mwuerms/tinytimer/microchip-studio/tinytimer/buttons.c

/**
 * Martin Egli
 * 2023-03-21
 * module timer
 */

#include <util/atomic.h>
#include <avr/interrupt.h>
#include "project.h"
#include "io.h"
#include "buttons.h"
#include "rtc.h"
#include "leds.h"

enum {
	BUTTON_NONE = 0,
	BUTTON_PRESSED,
	BUTTON_RELEASED
};
static volatile uint8_t button_last_state[NB_BUTTONS];

ISR(PORTA_PORT_vect) {
	if(BUTTON1_PORT.INTFLAGS & BUTTON1_PIN_BV) {
		BUTTON1_PORT.INTFLAGS |= BUTTON1_PIN_BV; // clr
		if(BUTTON1_PORT.IN & BUTTON1_PIN_BV) {
			button_last_state[BUTTON1] = BUTTON_RELEASED;
		}
		else {
			button_last_state[BUTTON1] = BUTTON_PRESSED;
		}
	}
	if(BUTTON2_PORT.INTFLAGS & BUTTON2_PIN_BV) {
		BUTTON2_PORT.INTFLAGS |= BUTTON2_PIN_BV; // clr
		if(BUTTON2_PORT.IN & BUTTON2_PIN_BV) {
			button_last_state[BUTTON2] = BUTTON_RELEASED;
		}
		else {
			button_last_state[BUTTON2] = BUTTON_PRESSED;
		}
	}
	global_events |= EV_BUTTON;
}

ISR(PORTB_PORT_vect) {
	if(BUTTON3_PORT.INTFLAGS & BUTTON3_PIN_BV) {
		BUTTON3_PORT.INTFLAGS |= BUTTON3_PIN_BV; // clr
		if(BUTTON3_PORT.IN & BUTTON3_PIN_BV) {
			button_last_state[BUTTON3] = BUTTON_RELEASED;
		}
		else {
			button_last_state[BUTTON3] = BUTTON_PRESSED;
		}
	}
	if(BUTTON4_PORT.INTFLAGS & BUTTON4_PIN_BV) {
		BUTTON4_PORT.INTFLAGS |= BUTTON4_PIN_BV; // clr
		if(BUTTON4_PORT.IN & BUTTON4_PIN_BV) {
			button_last_state[BUTTON4] = BUTTON_RELEASED;
		}
		else {
			button_last_state[BUTTON4] = BUTTON_PRESSED;
		}
	}
	global_events |= EV_BUTTON;
}

/* all buttons
 * input
 * pullup
 * interrupt on both edges
 * button pressed =  low,  falling edge
 * button released = high, rising edge
 */
#define PORT_INT_DISABLE	0
#define PORT_INT_BOTH_EDGES	1
void buttons_Init(void) {
	BUTTON1_PORT.DIRCLR = BUTTON1_PIN_BV;	// input
	BUTTON1_PORT.BUTTON1_PIN_CTRL = PORT_PULLUPEN_bm | PORT_INT_BOTH_EDGES;	// pullup, int on both edges
	
	BUTTON2_PORT.DIRCLR = BUTTON2_PIN_BV;
	BUTTON2_PORT.BUTTON2_PIN_CTRL = PORT_PULLUPEN_bm | PORT_INT_BOTH_EDGES;

	BUTTON3_PORT.DIRCLR = BUTTON3_PIN_BV;
	BUTTON3_PORT.BUTTON3_PIN_CTRL = PORT_PULLUPEN_bm | PORT_INT_BOTH_EDGES;

	BUTTON4_PORT.DIRCLR = BUTTON4_PIN_BV;
	BUTTON4_PORT.BUTTON4_PIN_CTRL = PORT_PULLUPEN_bm | PORT_INT_BOTH_EDGES;
}

#include "dbguart.h"

#define RTC_CNT_100ms	(uint16_t)(0.1*1024)  // 0.1s * 1024
#define RTC_CNT_1s		(1*1024) // 1.0s * 1024
#define RTC_CNT_2s		(2*1024) // 2.0s * 1024
static uint16_t button_rtc_cnt_pressed[NB_BUTTONS];
void button_ProcessEvent(void) {
	uint16_t rtc_cnt_value;
	uint8_t button_nb, proc_last_state;

	dbguart_SendString("BTN_EV ");
	ATOMIC_BLOCK(ATOMIC_RESTORESTATE) {
		rtc_cnt_value = rtc_GetCNT();
		for(button_nb = BUTTON1; button_nb < NB_BUTTONS; button_nb++) {
			// sync from background
			proc_last_state = button_last_state[button_nb];
			button_last_state[button_nb] = BUTTON_NONE;

			if(proc_last_state == BUTTON_PRESSED) {
				// falling edge: pressed
				button_rtc_cnt_pressed[button_nb] = rtc_cnt_value; // save to evaluate released
				dbguart_SendChar('P');
			}
			else if(proc_last_state == BUTTON_RELEASED) {
				// rising edge: released
				if(rtc_cnt_value > button_rtc_cnt_pressed[button_nb]) {
					rtc_cnt_value -= button_rtc_cnt_pressed[button_nb];
				}
				else {
					button_rtc_cnt_pressed[button_nb] -= rtc_cnt_value;
					rtc_cnt_value = button_rtc_cnt_pressed[button_nb];
				}
				dbguart_SendChar('R');

				if(rtc_cnt_value < RTC_CNT_100ms) {
					// too short, nothing to do
					break;
				}
				else if(rtc_cnt_value < RTC_CNT_1s) {
					ttimer_ProcessEvents(button_nb, TT_EV_BUTTON_SHORT_PRESSED);
				}
				else if(rtc_cnt_value < RTC_CNT_2s) {
					ttimer_ProcessEvents(button_nb, TT_EV_BUTTON_1s_LONG_PRESSED);
				}
				else {
					ttimer_ProcessEvents(button_nb, TT_EV_BUTTON_2s_LONG_PRESSED);
				}
			}
		}
	}
}
